orihikarna/Hermit/HermitB/dist.png

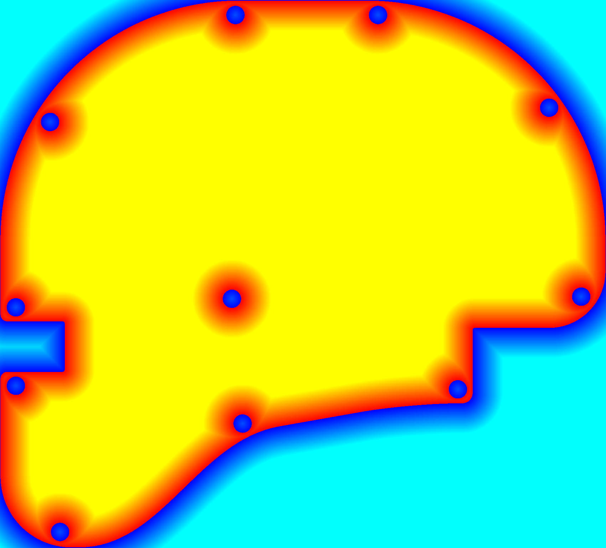
HermitB/dist.png
