orihikarna/Hermit/HermitT/dist.png

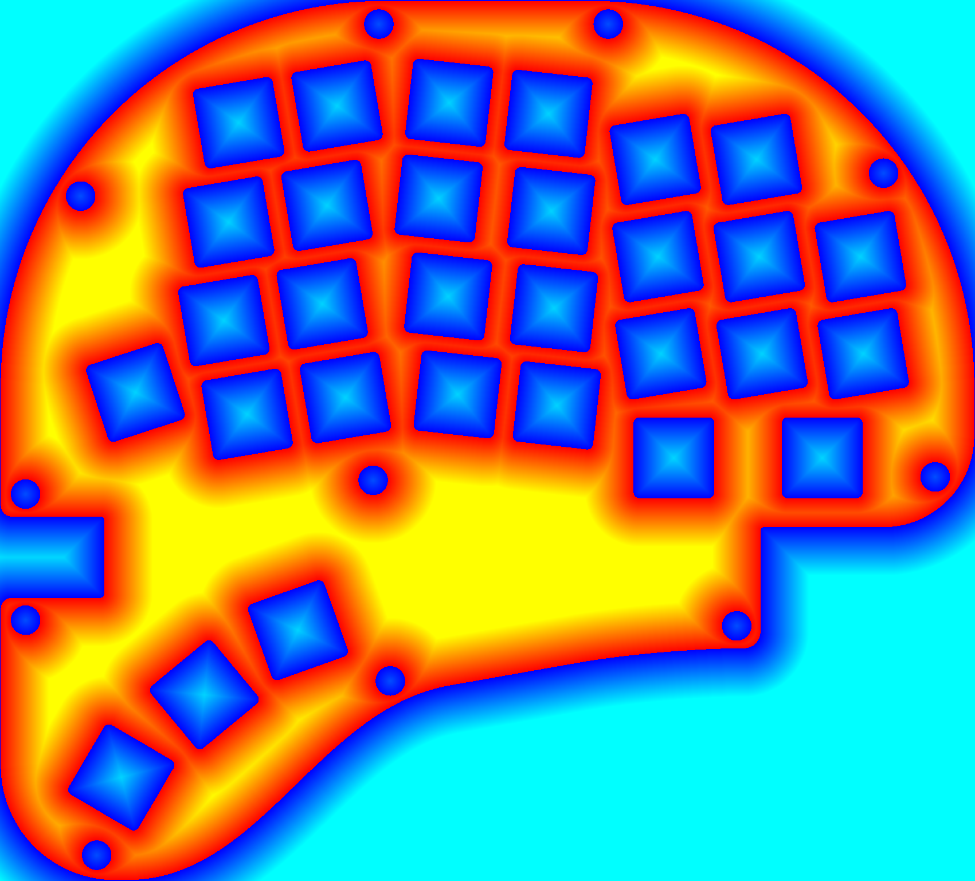
HermitT/dist.png
